bsgbsg7/Shiroe/Doc/3.50LCD插接40pin-ST7796-电容触摸技术资料/02-原理图/SPI接口.pdf

# 中景园电子3.5寸LCD显示屏SPI接口原理图

# 淘宝地址：http://shop73023976.taobao.com/?spm=a1z10.1.0.0.byBTLt&v=1

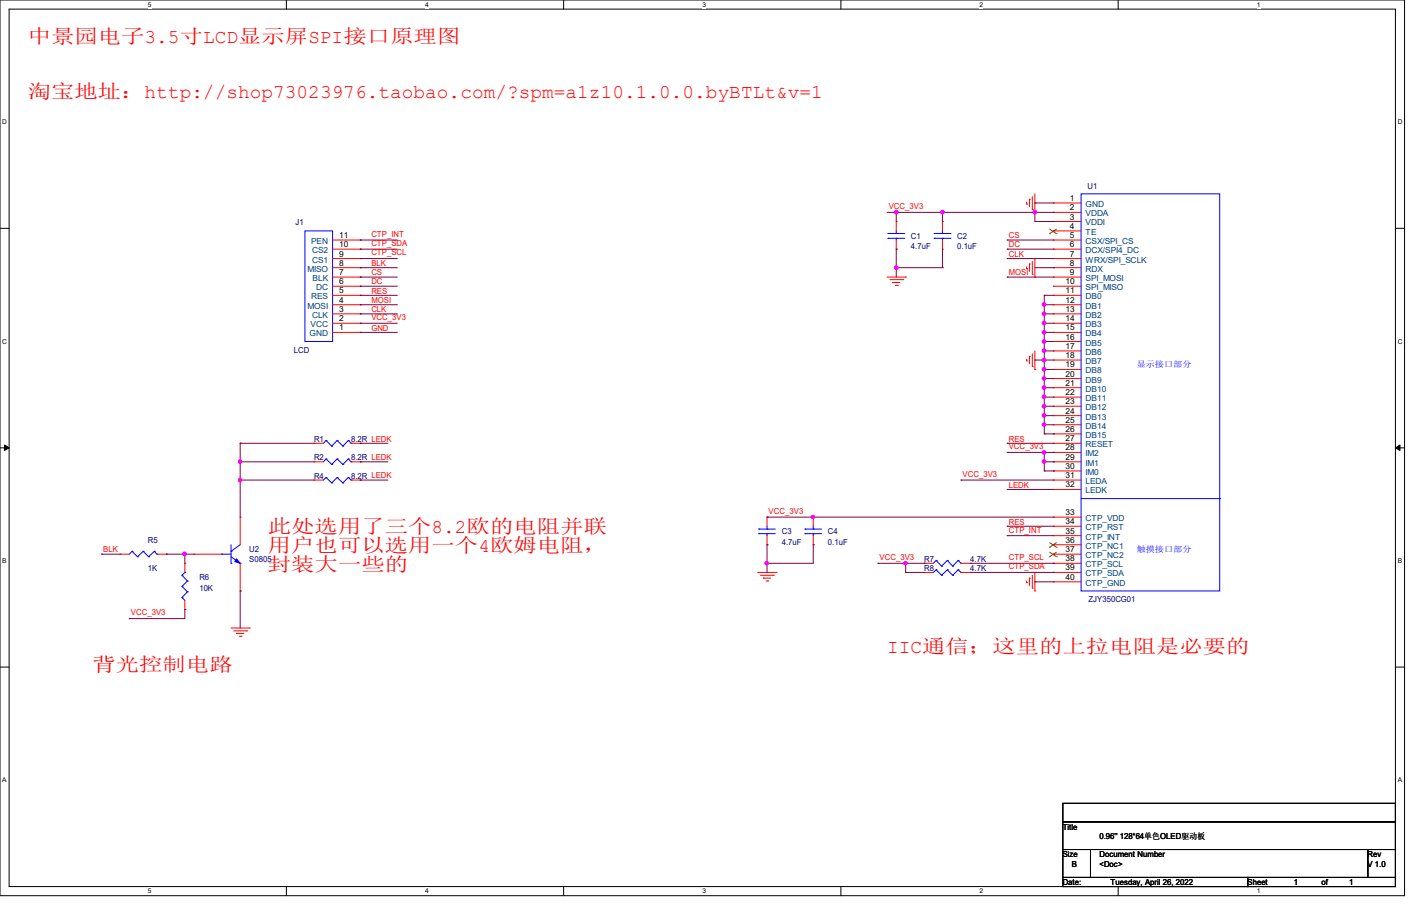
[picture p23: page 1]
