bsgbsg7/Shiroe/Doc/FPC4301MS-L190-40C-9A全套资料(1)/FPC4301MS-L190-40C-9A全套资料/FPC4301MS-L190-40C-9A外发资料/PCB/PCB4301MS V1.0.pdf

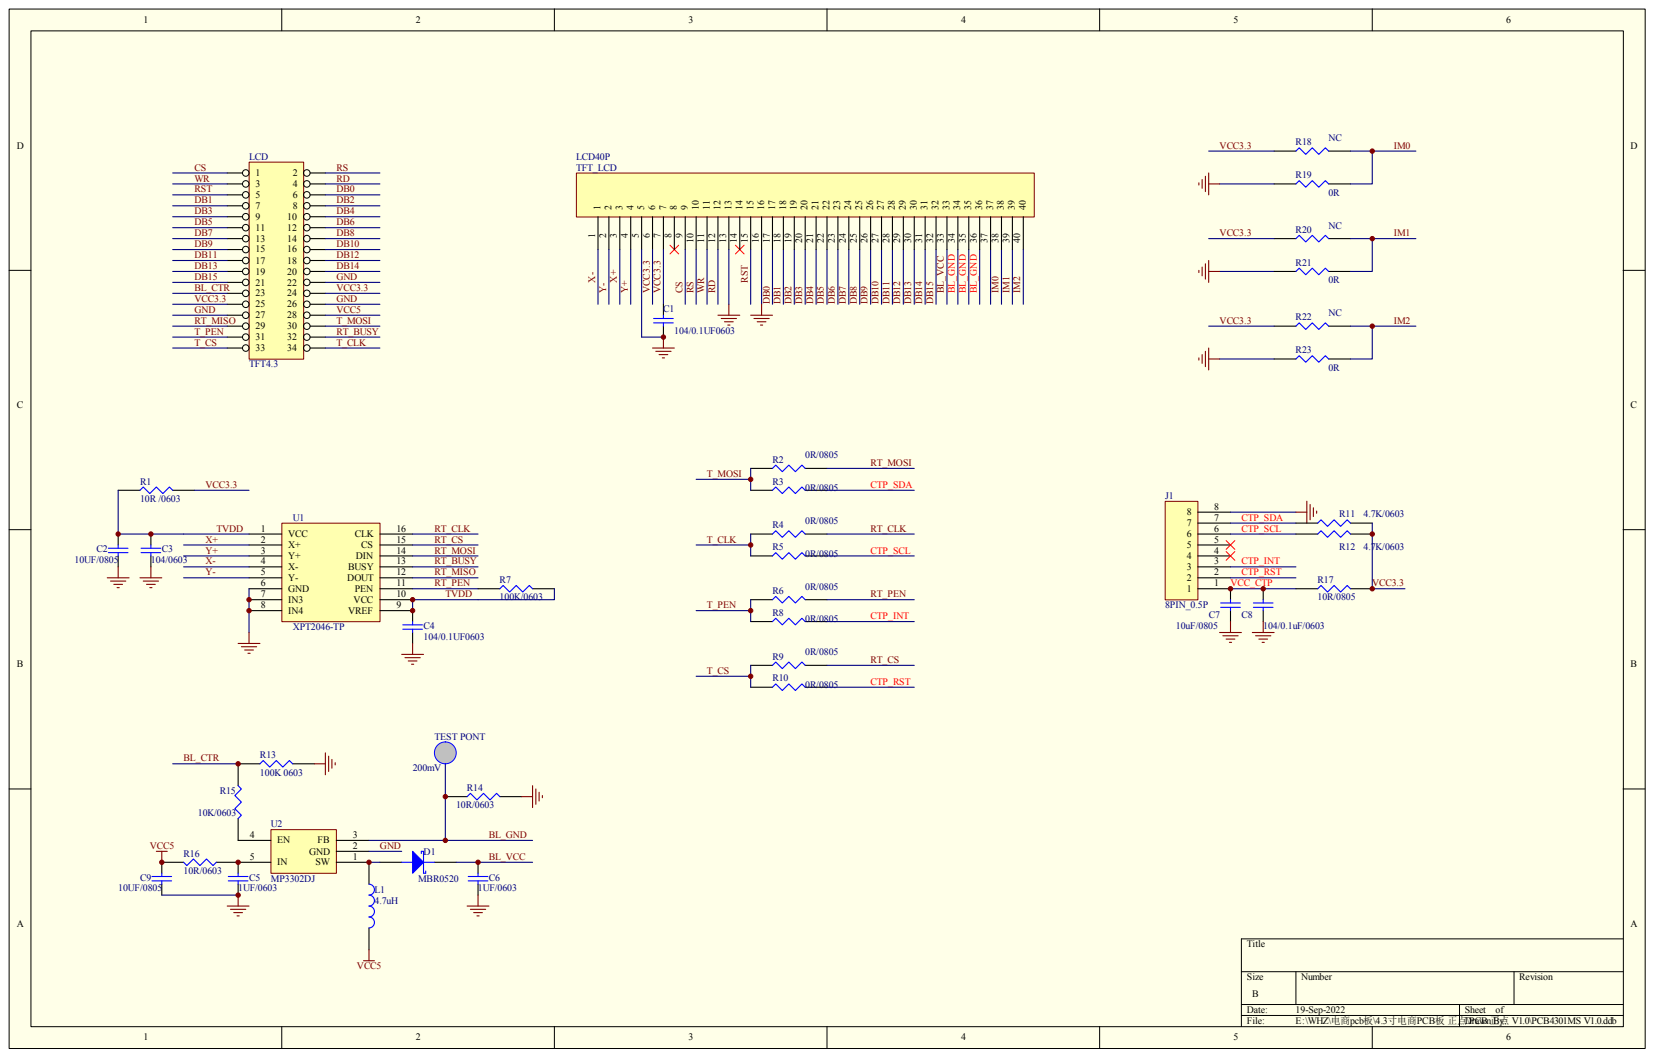
[picture p24: page 1]
