bsgbsg7/Shiroe/Software/src/app/music/music.cpp

#include "music.h"
double music_alarmFlag = 0;
lv_timer_t *music_alarm_timer;
void SendData(char addr) // 发送函数。
{

    digitalWrite(music_pin, HIGH); /*开始拉高*/
    delayMicroseconds(1000);
    digitalWrite(music_pin, LOW); /*开始引导码*/
    delayMicroseconds(3200);      /*此处延时最少要大于2ms*/
    for (int i = 0; i < 8; i++)   /*总共8位数据  */
    {
        digitalWrite(music_pin, HIGH);
        if (addr & 0x01) /*3:1表示数据位1,每个位用两个脉冲表示  */
        {
            delayMicroseconds(600);
            digitalWrite(music_pin, LOW);
            delayMicroseconds(200);
        }
        else /*1：3表示数据位0 ,每个位用两个脉冲表示  */
        {
            delayMicroseconds(200);
            digitalWrite(music_pin, LOW);
            delayMicroseconds(600);
        }
        addr >>= 1;
    }
    digitalWrite(music_pin, HIGH);
}

void show_number1()
{
    // 设置音量为20
    SendData(0x0a); // 清空数字
    SendData(0x09); // 音量20
    SendData(0x00);
    SendData(0x0c); // 设置音量
    delay(10);      // 延时

    // 选取曲目1播放
    SendData(0x0a); // 清空数字
    SendData(0x01); // 曲目数字，对应00001.mp3
    SendData(0x0b); // 选曲播放
    // delay(2000);

    // 开始播放
    // SendData(0x11);//开始播放
    // delay(2000);
}

void show_number2()
{
    // 设置音量为20
    SendData(0x0a); // 清空数字
    SendData(0x09); // 音量20
    SendData(0x00);
    SendData(0x0c); // 设置音量
    delay(10);      // 延时

    // 选取曲目2播放
    SendData(0x0a); // 清空数字
    SendData(0x02); // 曲目数字，对应00002.mp3
    SendData(0x0b); // 选曲播放

    // 开始播放
    // SendData(0x11);//开始播放,这部分可以没有
    // delay(2000);
}

void show_number3()
{
    // 设置音量为20
    SendData(0x0a); // 清空数字
    SendData(0x09); // 音量20
    SendData(0x00);
    SendData(0x0c); // 设置音量
    delay(10);      // 延时

    // 选取曲目2播放
    SendData(0x0a); // 清空数字
    SendData(0x03); // 曲目数字，对应00002.mp3
    SendData(0x0b); // 选曲播放

    // 开始播放
    // SendData(0x11);//开始播放,这部分可以没有
    // delay(2000);
}

static lv_obj_t *g_kb_screen;
static void kb_screen_event_cb(lv_event_t *e)
{
    lv_event_code_t code = lv_event_get_code(e);
    lv_obj_t *kb = lv_event_get_target(e);
    if (code == LV_EVENT_READY || code == LV_EVENT_CANCEL)
    {
        lv_obj_add_flag(kb, LV_OBJ_FLAG_HIDDEN);
    }
}
// static void ta_screen_event_cb(lv_event_t *e)
// {

// 	lv_event_code_t code = lv_event_get_code(e);
// 	lv_obj_t *ta = lv_event_get_target(e);
// 	lv_obj_t *kb = lv_event_get_user_data(e);
// 	if (code == LV_EVENT_FOCUSED || code == LV_EVENT_CLICKED)
// 	{
// 		lv_keyboard_set_textarea(kb, ta);
// 		lv_obj_move_foreground(kb);
// 		lv_obj_clear_flag(kb, LV_OBJ_FLAG_HIDDEN);
// 	}
// 	if (code == LV_EVENT_CANCEL || code == LV_EVENT_DEFOCUSED)
// 	{
// 		lv_keyboard_set_textarea(kb, NULL);
// 		lv_obj_move_background(kb);
// 		lv_obj_add_flag(kb, LV_OBJ_FLAG_HIDDEN);
// 	}
// }

lv_obj_t *alarm_load()
{
    // Write codes screen
    now_screen = lv_obj_create(NULL);

    // Create keyboard on screen
    lv_obj_t *g_kb_screen = lv_keyboard_create(now_screen);
    lv_obj_add_event_cb(g_kb_screen, kb_screen_event_cb, LV_EVENT_ALL, NULL);
    lv_obj_add_flag(g_kb_screen, LV_OBJ_FLAG_HIDDEN);
    lv_obj_set_style_text_font(g_kb_screen, &lv_font_montserrat_18, LV_PART_MAIN | LV_STATE_DEFAULT);
    lv_obj_set_scrollbar_mode(now_screen, LV_SCROLLBAR_MODE_OFF);

    // Set style for screen. Part: LV_PART_MAIN, State: LV_STATE_DEFAULT
    lv_obj_set_style_bg_color(now_screen, lv_color_make(0xff, 0xff, 0xff), LV_PART_MAIN | LV_STATE_DEFAULT);
    lv_obj_set_style_bg_grad_color(now_screen, lv_color_make(0x21, 0x95, 0xf6), LV_PART_MAIN | LV_STATE_DEFAULT);
    lv_obj_set_style_bg_grad_dir(now_screen, LV_GRAD_DIR_NONE, LV_PART_MAIN | LV_STATE_DEFAULT);
    lv_obj_set_style_bg_opa(now_screen, 0, LV_PART_MAIN | LV_STATE_DEFAULT);

    // Write codes screen_img_1
    lv_obj_t *screen_img_1 = lv_img_create(now_screen);
    lv_obj_set_pos(screen_img_1, 296, 21);
    lv_obj_set_size(screen_img_1, 155, 160);
    lv_obj_set_scrollbar_mode(screen_img_1, LV_SCROLLBAR_MODE_OFF);

    // Set style for screen_img_1. Part: LV_PART_MAIN, State: LV_STATE_DEFAULT
    lv_obj_set_style_img_recolor(screen_img_1, lv_color_make(0xff, 0xff, 0xff), LV_PART_MAIN | LV_STATE_DEFAULT);
    lv_obj_set_style_img_recolor_opa(screen_img_1, 0, LV_PART_MAIN | LV_STATE_DEFAULT);
    lv_obj_set_style_img_opa(screen_img_1, 255, LV_PART_MAIN | LV_STATE_DEFAULT);
    lv_obj_add_flag(screen_img_1, LV_OBJ_FLAG_CLICKABLE);
    lv_img_set_src(screen_img_1, &_1_alpha_155x160);
    lv_img_set_pivot(screen_img_1, 50, 50);
    lv_img_set_angle(screen_img_1, 0);

    // Write codes screen_label_1
    lv_obj_t *screen_label_1 = lv_label_create(now_screen);
    lv_obj_set_pos(screen_label_1, 56, 44);
    lv_obj_set_size(screen_label_1, 183, 115);
    lv_obj_set_scrollbar_mode(screen_label_1, LV_SCROLLBAR_MODE_OFF);
    lv_label_set_text(screen_label_1, "闹钟警报");
    lv_label_set_long_mode(screen_label_1, LV_LABEL_LONG_WRAP);

    // Set style for screen_label_1. Part: LV_PART_MAIN, State: LV_STATE_DEFAULT
    lv_obj_set_style_radius(screen_label_1, 0, LV_PART_MAIN | LV_STATE_DEFAULT);
    lv_obj_set_style_bg_color(screen_label_1, lv_color_make(0xff, 0xff, 0xff), LV_PART_MAIN | LV_STATE_DEFAULT);
    lv_obj_set_style_bg_grad_color(screen_label_1, lv_color_make(0x21, 0x95, 0xf6), LV_PART_MAIN | LV_STATE_DEFAULT);
    lv_obj_set_style_bg_grad_dir(screen_label_1, LV_GRAD_DIR_NONE, LV_PART_MAIN | LV_STATE_DEFAULT);
    lv_obj_set_style_bg_opa(screen_label_1, 255, LV_PART_MAIN | LV_STATE_DEFAULT);
    lv_obj_set_style_shadow_width(screen_label_1, 0, LV_PART_MAIN | LV_STATE_DEFAULT);
    lv_obj_set_style_shadow_color(screen_label_1, lv_color_make(0x21, 0x95, 0xf6), LV_PART_MAIN | LV_STATE_DEFAULT);
    lv_obj_set_style_shadow_opa(screen_label_1, 255, LV_PART_MAIN | LV_STATE_DEFAULT);
    lv_obj_set_style_shadow_spread(screen_label_1, 0, LV_PART_MAIN | LV_STATE_DEFAULT);
    lv_obj_set_style_shadow_ofs_x(screen_label_1, 0, LV_PART_MAIN | LV_STATE_DEFAULT);
    lv_obj_set_style_shadow_ofs_y(screen_label_1, 0, LV_PART_MAIN | LV_STATE_DEFAULT);
    lv_obj_set_style_text_color(screen_label_1, lv_color_make(0xe7, 0x08, 0x08), LV_PART_MAIN | LV_STATE_DEFAULT);
    lv_obj_set_style_text_font(screen_label_1, &lv_chinese_font_24_all, LV_PART_MAIN | LV_STATE_DEFAULT);
    lv_obj_set_style_text_letter_space(screen_label_1, 2, LV_PART_MAIN | LV_STATE_DEFAULT);
    lv_obj_set_style_text_line_space(screen_label_1, 0, LV_PART_MAIN | LV_STATE_DEFAULT);
    lv_obj_set_style_text_align(screen_label_1, LV_TEXT_ALIGN_CENTER, LV_PART_MAIN | LV_STATE_DEFAULT);
    lv_obj_set_style_pad_left(screen_label_1, 0, LV_PART_MAIN | LV_STATE_DEFAULT);
    lv_obj_set_style_pad_right(screen_label_1, 0, LV_PART_MAIN | LV_STATE_DEFAULT);
    lv_obj_set_style_pad_top(screen_label_1, 44, LV_PART_MAIN | LV_STATE_DEFAULT);
    lv_obj_set_style_pad_bottom(screen_label_1, 0, LV_PART_MAIN | LV_STATE_DEFAULT);

    // Write codes screen_btn_1
    lv_obj_t *screen_btn_1 = lv_btn_create(now_screen);
    lv_obj_set_pos(screen_btn_1, 288, 205);
    lv_obj_set_size(screen_btn_1, 118, 66);
    lv_obj_set_scrollbar_mode(screen_btn_1, LV_SCROLLBAR_MODE_OFF);

    // Set style for screen_btn_1. Part: LV_PART_MAIN, State: LV_STATE_DEFAULT
    lv_obj_set_style_radius(screen_btn_1, 5, LV_PART_MAIN | LV_STATE_DEFAULT);
    lv_obj_set_style_bg_color(screen_btn_1, lv_color_make(0x21, 0x95, 0xf6), LV_PART_MAIN | LV_STATE_DEFAULT);
    lv_obj_set_style_bg_grad_color(screen_btn_1, lv_color_make(0x21, 0x95, 0xf6), LV_PART_MAIN | LV_STATE_DEFAULT);
    lv_obj_set_style_bg_grad_dir(screen_btn_1, LV_GRAD_DIR_NONE, LV_PART_MAIN | LV_STATE_DEFAULT);
    lv_obj_set_style_bg_opa(screen_btn_1, 255, LV_PART_MAIN | LV_STATE_DEFAULT);
    lv_obj_set_style_shadow_width(screen_btn_1, 0, LV_PART_MAIN | LV_STATE_DEFAULT);
    lv_obj_set_style_shadow_color(screen_btn_1, lv_color_make(0x21, 0x95, 0xf6), LV_PART_MAIN | LV_STATE_DEFAULT);
    lv_obj_set_style_shadow_opa(screen_btn_1, 255, LV_PART_MAIN | LV_STATE_DEFAULT);
    lv_obj_set_style_shadow_spread(screen_btn_1, 0, LV_PART_MAIN | LV_STATE_DEFAULT);
    lv_obj_set_style_shadow_ofs_x(screen_btn_1, 0, LV_PART_MAIN | LV_STATE_DEFAULT);
    lv_obj_set_style_shadow_ofs_y(screen_btn_1, 0, LV_PART_MAIN | LV_STATE_DEFAULT);
    lv_obj_set_style_border_color(screen_btn_1, lv_color_make(0x21, 0x95, 0xf6), LV_PART_MAIN | LV_STATE_DEFAULT);
    lv_obj_set_style_border_width(screen_btn_1, 0, LV_PART_MAIN | LV_STATE_DEFAULT);
    lv_obj_set_style_border_opa(screen_btn_1, 255, LV_PART_MAIN | LV_STATE_DEFAULT);
    lv_obj_set_style_text_color(screen_btn_1, lv_color_make(0xff, 0xff, 0xff), LV_PART_MAIN | LV_STATE_DEFAULT);
    lv_obj_set_style_text_font(screen_btn_1, &lv_chinese_font_24_all, LV_PART_MAIN | LV_STATE_DEFAULT);
    lv_obj_set_style_text_align(screen_btn_1, LV_TEXT_ALIGN_CENTER, LV_PART_MAIN | LV_STATE_DEFAULT);
    lv_obj_t *screen_btn_1_label = lv_label_create(screen_btn_1);
    lv_label_set_text(screen_btn_1_label, "关闭");
    lv_obj_set_style_pad_all(screen_btn_1, 0, LV_STATE_DEFAULT);
    lv_obj_align(screen_btn_1_label, LV_ALIGN_CENTER, 0, 0);

    // Write codes screen_btn_2
    lv_obj_t *screen_btn_2 = lv_btn_create(now_screen);
    lv_obj_set_pos(screen_btn_2, 88, 205);
    lv_obj_set_size(screen_btn_2, 118, 66);
    lv_obj_set_scrollbar_mode(screen_btn_2, LV_SCROLLBAR_MODE_OFF);

    // Set style for screen_btn_2. Part: LV_PART_MAIN, State: LV_STATE_DEFAULT
    lv_obj_set_style_radius(screen_btn_2, 5, LV_PART_MAIN | LV_STATE_DEFAULT);
    lv_obj_set_style_bg_color(screen_btn_2, lv_color_make(0x21, 0x95, 0xf6), LV_PART_MAIN | LV_STATE_DEFAULT);
    lv_obj_set_style_bg_grad_color(screen_btn_2, lv_color_make(0x21, 0x95, 0xf6), LV_PART_MAIN | LV_STATE_DEFAULT);
    lv_obj_set_style_bg_grad_dir(screen_btn_2, LV_GRAD_DIR_NONE, LV_PART_MAIN | LV_STATE_DEFAULT);
    lv_obj_set_style_bg_opa(screen_btn_2, 255, LV_PART_MAIN | LV_STATE_DEFAULT);
    lv_obj_set_style_shadow_width(screen_btn_2, 0, LV_PART_MAIN | LV_STATE_DEFAULT);
    lv_obj_set_style_shadow_color(screen_btn_2, lv_color_make(0x21, 0x95, 0xf6), LV_PART_MAIN | LV_STATE_DEFAULT);
    lv_obj_set_style_shadow_opa(screen_btn_2, 255, LV_PART_MAIN | LV_STATE_DEFAULT);
    lv_obj_set_style_shadow_spread(screen_btn_2, 0, LV_PART_MAIN | LV_STATE_DEFAULT);
    lv_obj_set_style_shadow_ofs_x(screen_btn_2, 0, LV_PART_MAIN | LV_STATE_DEFAULT);
    lv_obj_set_style_shadow_ofs_y(screen_btn_2, 0, LV_PART_MAIN | LV_STATE_DEFAULT);
    lv_obj_set_style_border_color(screen_btn_2, lv_color_make(0x21, 0x95, 0xf6), LV_PART_MAIN | LV_STATE_DEFAULT);
    lv_obj_set_style_border_width(screen_btn_2, 0, LV_PART_MAIN | LV_STATE_DEFAULT);
    lv_obj_set_style_border_opa(screen_btn_2, 255, LV_PART_MAIN | LV_STATE_DEFAULT);
    lv_obj_set_style_text_color(screen_btn_2, lv_color_make(0xff, 0xff, 0xff), LV_PART_MAIN | LV_STATE_DEFAULT);
    lv_obj_set_style_text_font(screen_btn_2, &lv_chinese_font_24_all, LV_PART_MAIN | LV_STATE_DEFAULT);
    lv_obj_set_style_text_align(screen_btn_2, LV_TEXT_ALIGN_CENTER, LV_PART_MAIN | LV_STATE_DEFAULT);
    lv_obj_t *screen_btn_2_label = lv_label_create(screen_btn_2);
    lv_label_set_text(screen_btn_2_label, "推迟");
    lv_obj_set_style_pad_all(screen_btn_2, 0, LV_STATE_DEFAULT);
    lv_obj_align(screen_btn_2_label, LV_ALIGN_CENTER, 0, 0);

    lv_obj_add_event_cb(screen_btn_1, alarm_cancel_event, LV_EVENT_CLICKED, NULL);
    music_alarm_change();
    music_alarm_timer = lv_timer_create(music_alarm_timer_cb, 10000, NULL);
    return now_screen;
}

void alarm_cancel_event(lv_event_t *e)
{
    SendData(0x13);
    lv_timer_del(music_alarm_timer);
    app_return(LV_SCR_LOAD_ANIM_MOVE_RIGHT, 200, 20);
}

void music_alarm_change()
{
    if (music_choose_flag == 0)
    {
        show_number1();
    }
    else if (music_choose_flag == 1)
    {
        show_number2();
    }
    else if (music_choose_flag == 2)
    {
        show_number3();
    }

    Serial.println("THIS IS THE TIMER");
}

void music_alarm_timer_cb(lv_timer_t *timer)
{
    music_alarm_change();
}
