bsgbsg7/Shiroe/Doc/FPC4301MS-L190-40C-9A全套资料(1)/FPC4301MS-L190-40C-9A全套资料/FPC4301MS-L190-40C-9A外发资料/LCM/C51调试例程/KM200_MCU8bit_FPC4301MS-L190-40C-9A_HX8369A_LG4.3/lcd/lcd.h

#include "c8051F340.h"
#include <main.h>

#ifndef __LCD_h__
#define __LCD_h__

#ifdef DEBUG
#define END 0xffff
#endif

extern unsigned int code pic_eval[];
extern unsigned char code ascii[]; 
extern unsigned int code debug_code[50][15];

#define PIC_WIDTH    160	 //预备向LCD显示区域填充的图片的大小
#define PIC_HEIGHT   160

	#define  FONT_W  8
	#define  FONT_H  16


//---------------------------------------------------------------------
void WriteComm(uint8 i);
void WriteData(uint8 i);
//void SPI_SendData(unsigned char i);
unsigned char SPI_SendData(unsigned char i);
void WriteDispData(unsigned char DataH,unsigned char DataL);
void LCD_Init(void);
void BlockWrite(unsigned int Xstart,unsigned int Xend,unsigned int Ystart,unsigned int Yend) reentrant;
void DispBand(void);
void DispColor(unsigned int color);
void DispFrame(void);
void DispPic(unsigned int code *picture);
void DispPicFromSD(unsigned char PicNum);

void DispScaleHor1(void);
void DispScaleVer(void);
void DispScaleVer_Red(void);
void DispScaleVer_Green(void);
void DispScaleVer_Blue(void);
void DispScaleVer_Gray(void);
void DispGrayHor16(void);
void DispGrayHor32(void);
void DispScaleHor2(void);
void DispSnow(void);
void DispBlock(void);
void sleep(void);

void WriteOneDot(unsigned int color);
unsigned char ToOrd(unsigned char ch); 
void DispOneChar(unsigned char ord,unsigned int Xstart,unsigned int Ystart,unsigned int TextColor,unsigned int BackColor);	 // ord:0~95
void DispStr(unsigned char *str,unsigned int Xstart,unsigned int Ystart,unsigned int TextColor,unsigned int BackColor);
void DispInt(unsigned int i,unsigned int Xstart,unsigned int Ystart,unsigned int TextColor,unsigned int BackColor);

unsigned int ReadData(void);
void DispRegValue(unsigned int RegIndex,unsigned char ParNum);
void Disp_ID_Lcd(void);
void Disp_ID_clr(void);
void Debug(void);

void PutPixel(unsigned int x,unsigned int y,unsigned int color);
void DrawLine(unsigned int Xstart,unsigned int Xend,unsigned int Ystart,unsigned int Yend,unsigned int color);
void DrawGird(unsigned int color);
void Disp_Pro_Name(void);
#endif
