bsgbsg7/Shiroe/Doc/FPC4301MS-L190-40C-9A全套资料(1)/FPC4301MS-L190-40C-9A全套资料/FPC4301MS-L190-40C-9A外发资料/LCM/C51调试例程/KM200_MCU8bit_FPC4301MS-L190-40C-9A_HX8369A_LG4.3/mmc_sd/mmc_sd.h

//#include<main.h>

#ifndef __MMC_SD_h__
#define __MMC_SD_h__

#define SPI_CS_Assert()    NSSMD0   = 0;   
#define SPI_CS_Deassert()  NSSMD0   = 1;  

//extern unsigned char xdata buffer[512];

extern void  SD_Init(void);
extern unsigned char MMC_SD_ReadSingleBlock(unsigned long sector);
extern unsigned char MMC_SD_WriteSingleBlock(unsigned long sector);
extern unsigned char MMC_SD_SendCommand(unsigned char cmd, unsigned long arg);
extern unsigned char SPI_WriteByte(unsigned char val);

#endif
