bsgbsg7/Shiroe/Software/src/app/lunar/lunarCalender.h

// #pragma once

// // #include "head.h"


// #ifdef __cplusplus
// extern "C" {
// #endif
// /*********************
// *      INCLUDES
// *********************/

// /*********************
// *      DEFINES
// *********************/


// /**********************
// *      TYPEDEFS
// **********************/


// // int8_t Calc_24SolarTerms(uint16_t SolarYear, uint8_t *Array_24SolarTermDate);
// int8_t Solar2Lunar(Solar_t *so, Lunar_t *lu);
// // int8_t Calc_Lunar_From_DateInterval(uint32_t DateInterval, Lunar_t *LU);
// // int8_t Calc_thisLunarMonth_Days(uint16_t SolarYear, uint8_t LunarMonth);
// // int8_t Calc_thisLunarYear_HasLeapMonth(uint16_t SolarYear, Lunar_t *Lunar);
// // uint8_t IsLeapYear(uint16_t year);
// // uint32_t Calc_Solar_DateInterval(Solar_t *Solar1, Solar_t *Solar2);


// #ifdef __cplusplus
// } /* extern "C" */
// #endif
