bsgbsg7/Shiroe/Software/src/study/sk6812.h

// #ifndef __SK6812_H_
// #define __SK6812_H_

// #ifdef __cplusplus
// extern "C" {
// #endif

// #ifndef BRIGHTNESS  
// #define BRIGHTNESS  50
// #endif

// #ifndef LED_TYPE   
// #define LED_TYPE    SK6812
// #endif

// #ifndef COLOR_ORDER 
// #define COLOR_ORDER GRB
// #endif

// #ifndef UPDATES_PER_SECOND 
// #define UPDATES_PER_SECOND 100
// #endif

// void SK6812Loop();
// void SK6812Init();
// void ChangePalettePeriodically();
// void FillLEDsFromPaletteColors( uint8_t colorIndex);
// void SetupPurpleAndGreenPalette();
// void SetupBlackAndWhiteStripedPalette();
// void SetupTotallyRandomPalette();


// // #include "common.h"
// // #include <Arduino.h>
// // #include "study/ws2812.h"

// // void setup()
// // {
// //     Serial.begin( 115200 ); /* prepare for possible serial debug */
// //     WS2812BInit();
// // }

// // void loop()
// // {
// //   WS2812BLoop();
// //   delay(500);
// // }


// #ifdef __cplusplus
// } /* extern "C" */
// #endif

// #endif
