bsgbsg7/Shiroe/Software/src/study/weather.h

// #ifndef __WEATHER_H_
// #define __WEATHER_H_



// #include <ArduinoJson.h>
// #include <Arduino.h>
// #include "lvgl.h"
// #include "examples/lv_examples.h"
// #include "demos/lv_demos.h"

// #ifdef __cplusplus
// extern "C" {
// #endif

// /*********************
// *      INCLUDES
// *********************/

// /*********************
// *      DEFINES
// *********************/


// /**********************
// *      TYPEDEFS
// **********************/

// /**********************
// * GLOBAL PROTOTYPES
// **********************/

// typedef struct weatherinfo {
//     String city;
//     String temperature;
//     String updateDate;
// } weather_info_t;

// extern int getIconCode(String cond_code);
// extern void updateWeather(weather_info_t *data, String key, String location);

// /**********************
// *      MACROS
// **********************/

// #ifdef __cplusplus
// } /* extern "C" */
// #endif


// #endif
