bsgbsg7/Shiroe/Software/src/study/wifiscan.h

// #ifndef __WIFISCAN_H_
// #define __WIFISCAN_H_


// #ifdef __cplusplus
// extern "C" {
// #endif

// /*********************
// *      INCLUDES
// *********************/

// /*********************
// *      DEFINES
// *********************/
// #include <Arduino.h>
// #include "lvgl.h"
// #include "examples/lv_examples.h"
// #include "demos/lv_demos.h"
// /**********************
// *      TYPEDEFS
// **********************/

// /**********************
// * GLOBAL PROTOTYPES
// **********************/
// typedef enum wifi_state
// {
//     WIFI_STATE_OPENED,
//     WIFI_STATE_CLOSED,
// } wifi_state_t;

// extern void wifi_init(void);
// extern void wifi_begin(void);
// extern void wifi_stop(void);

// /**********************
// *      MACROS
// **********************/

// #ifdef __cplusplus
// } /* extern "C" */
// #endif


// #endif
