bsgbsg7/Shiroe/Software/src/myGuiStudy.h

#ifndef __MYGUISTUDY__H__
#define __MYGUISTUDY__H__

#ifdef __cplusplus
extern "C" {
#endif

// #include <lvgl.h>
// #include <lv_demo.h>
// #include "../lvgl/examples/lv_examples.h"

// void lv_example_bar_6(void);

int test2(int x,int y);

#ifdef __cplusplus
} /*extern "C"*/
#endif

#endif
